nightowl3090/OGX-LIVE/images/20250701_231221.jpg

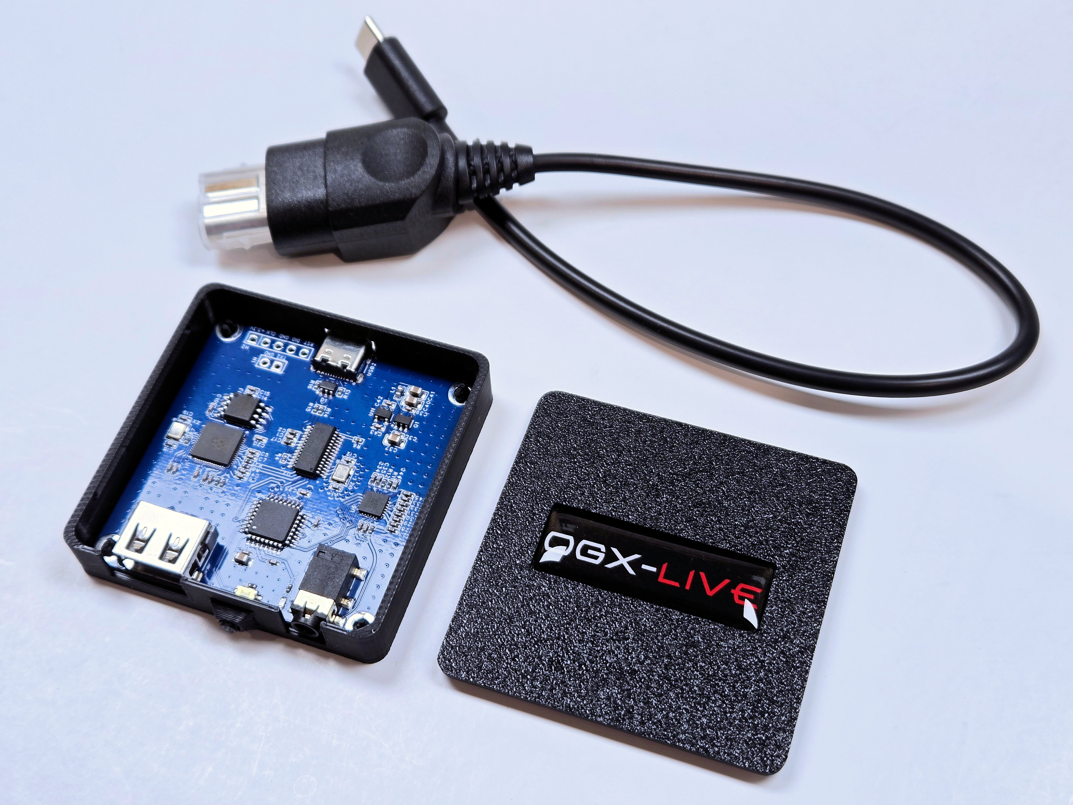
images/20250701_231221.jpg
